demonlibra/smart_ssr/kicad/smart-ssr.kicad_sch

## KiCad design kicad/smart-ssr.kicad_sch (2023-09-03)

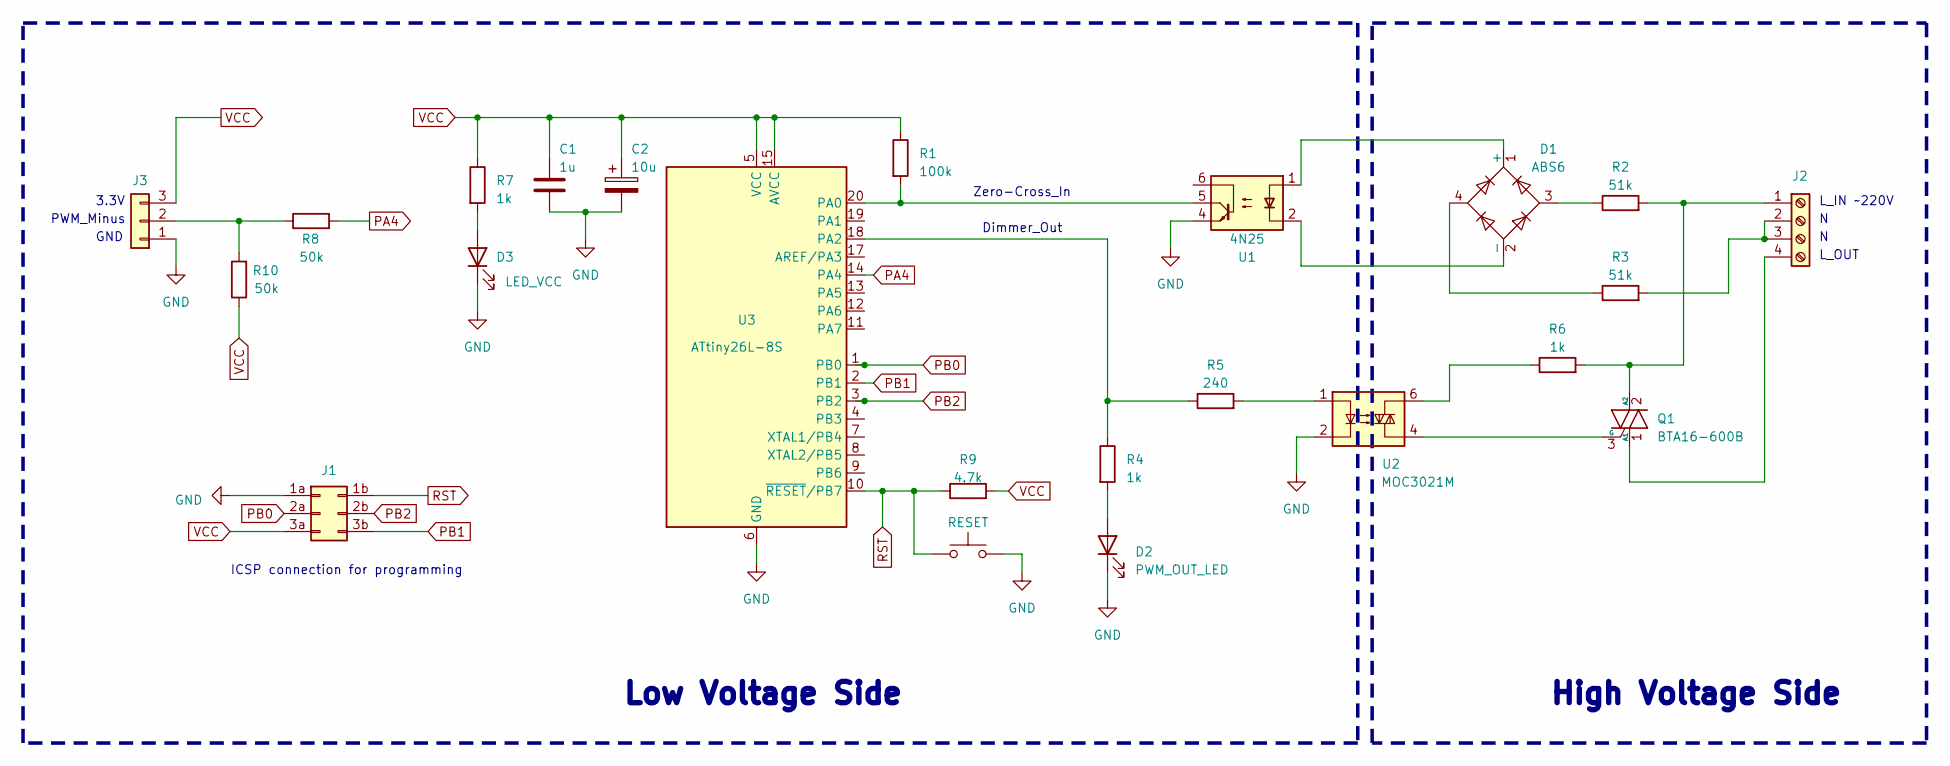
[picture p12: schematic smart-ssr.kicad_sch]

Parts:
C1: 1u
C2: 10u
D1: ABS6; Diode_Bridge_Diotec_ABS
D2: PWM_OUT_LED; LED_0603_1608Metric_Pad1.05x0.95mm_HandSolder
D3: LED_VCC; LED_0603_1608Metric_Pad1.05x0.95mm_HandSolder
J1: Conn_02x03_Row_Letter_Last; PinHeader_2x03_P2.54mm_Vertical
J2: Screw_Terminal_01x04; TerminalBlock_MetzConnect_Type067_RT01904HDWC_1x04_P10.00mm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
J3: Conn_01x03; JST_XH_B3B-XH-A_1x03_P2.50mm_Vertical
Q1: BTA16-600B; TO-220-3_Vertical
R1: 100k
R2, R3: 51k
R4, R6, R7: 1k
R5: 240
R8, R10: 50k
R9: 4.7k
RESET: SW_Push; SW_Tactile_SPST_NO_Straight_CK_PTS636Sx25SMTRLFS
U1: 4N25; DIP-6_W7.62mm
U2: MOC3021M
U3: ATtiny26L-8S; SOIC-20W_7.5x12.8mm_P1.27mm

Connections:
GND: C1.2, C2.2, D2.1 (K), D3.1 (K), J1.1a, J3.1, RESET.2, U1.4, U2.2, U3.6 (GND), U3.16 (GND)
unnamed: D1.1 (+), U1.1
unnamed: D1.2 (-), U1.2
unnamed: D1.3, R2.1
unnamed: D1.4, R3.1
unnamed: D2.2 (A), R4.2
unnamed: D3.2 (A), R7.2
unnamed: J2.1, Q1.2 (A2), R2.2, R6.2
unnamed: J2.2, J2.3, R3.2
unnamed: J2.4, Q1.1 (A1)
unnamed: J3.2, R8.1, R10.2
unnamed: Q1.3 (G), U2.4
unnamed: R1.2, U1.5, U3.20 (PA0)
unnamed: R4.1, R5.1, U3.18 (PA2)
unnamed: R5.2, U2.1
unnamed: R6.1, U2.6
PA4: R8.2, U3.14 (PA4)
PB0: J1.2a, U3.1 (PB0)
PB1: J1.3b, U3.2 (PB1)
PB2: J1.2b, U3.3 (PB2)
RST: J1.1b, R9.1, RESET.1, U3.10 (~RESET/PB7)
VCC: C1.1, C2.1, J1.3a, J3.3, R1.1, R7.1, R9.2, R10.1, U3.5 (VCC), U3.15 (AVCC)

Notes on the sheet:
Dimmer_Out
L_OUT
Low Voltage Side
L_IN ~220V
GND
ICSP connection for programming
3.3V
PWM_Minus
High Voltage Side
Zero-Cross_In
